jorisroovers/window-opener/diagrams/kicad/window-opener-relay/window-opener-relay.sch

## KiCad design diagrams/kicad/window-opener-relay/window-opener-relay.sch (2020-07-16)

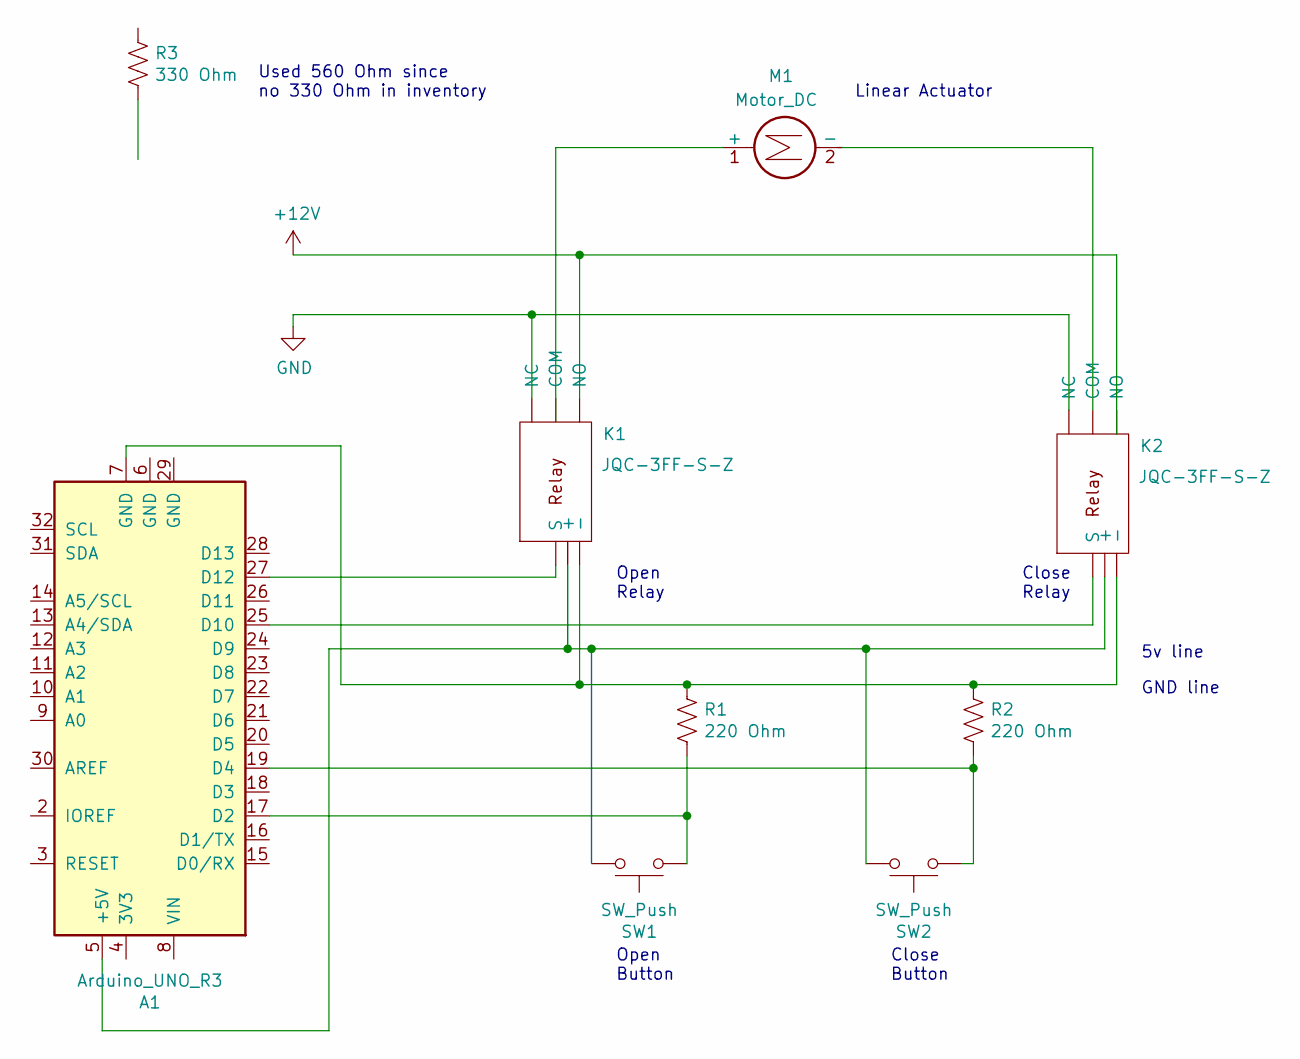
[picture p23: schematic window-opener-relay.sch]

Parts:
A1: Arduino_UNO_R3
K1, K2: JQC-3FF-S-Z
M1: Motor_DC
R1, R2: 220 Ohm
R3: 330 Ohm
SW1, SW2: SW_Push

Connections:
+12V: K2.~
unnamed: A1.5 (+5V), K1.~, K2.~, SW1.2, SW2.2
unnamed: A1.7 (GND), K1.~, K2.~, R1.1, R2.1
unnamed: A1.17 (D2), R1.2, SW1.1
unnamed: A1.19 (D4), R2.2, SW2.1
unnamed: A1.25 (D10), K2.~
unnamed: A1.27 (D12), K1.~
unnamed: K1.~, M1.1 (+)

Notes on the sheet:
GND line
5v line
Close Button
Open Button
Linear Actuator
Open Relay
Close Relay
Used 560 Ohm since no 330 Ohm in inventory
